hierle/letterbox-sensor-v2/letterbox-sensor-v2/lorawan.h

//
// lorawan.h
//

// region
#define LORAWAN_BAND     (RAK_REGION_EU868)

// ABP settings
#define ABP_DEVADDR  {0x00, 0x01, 0x02, 0x03}
#define ABP_NWKSKEY  {0x00, 0x01, 0x02, 0x03, 0x04, 0x05, 0x06, 0x07, 0x08, 0x09, 0x0a, 0x0b, 0x0c, 0x0d, 0x0e, 0x0f}
#define ABP_APPSKEY  {0x00, 0x01, 0x02, 0x03, 0x04, 0x05, 0x06, 0x07, 0x08, 0x09, 0x0a, 0x0b, 0x0c, 0x0d, 0x0e, 0x0f}

// OTAA settings
#define OTAA_DEVEUI  {0x00, 0x01, 0x02, 0x03, 0x04, 0x05, 0x06, 0x07}
// APPEUI or JOINEUI, identifying the join server
#define OTAA_APPEUI  {0x00, 0x01, 0x02, 0x03, 0x04, 0x05, 0x06, 0x07}
#define OTAA_APPKEY  {0x00, 0x01, 0x02, 0x03, 0x04, 0x05, 0x06, 0x07, 0x08, 0x09, 0x0a, 0x0b, 0x0c, 0x0d, 0x0e, 0x0f}
